socalphil/IC705BTXPA125B/UNVR67X12pt7b.h

const uint8_t UNVR67X12pt7bBitmaps[] PROGMEM = {
  0x00, 0xFF, 0xFF, 0xFF, 0xFF, 0xF0, 0x3F, 0xE0, 0xEF, 0xDF, 0xBF, 0x7E,
  0xFD, 0xC0, 0x03, 0x30, 0x77, 0x06, 0x60, 0x66, 0x0C, 0xC3, 0xFF, 0x3F,
  0xF1, 0x98, 0x19, 0x81, 0x98, 0x33, 0x0F, 0xFC, 0xFF, 0xC6, 0x60, 0x66,
  0x0E, 0xE0, 0xCC, 0x00, 0x18, 0x18, 0x18, 0x3E, 0xFF, 0xE7, 0xE7, 0xF0,
  0x7C, 0x1E, 0x0F, 0xE7, 0xE7, 0xFF, 0x7C, 0x18, 0x18, 0x18, 0x78, 0x63,
  0xF1, 0x8C, 0xC6, 0x33, 0x30, 0xCC, 0xC3, 0x36, 0x0C, 0xD8, 0x3F, 0x60,
  0x7B, 0x78, 0x0F, 0xF0, 0x6C, 0xC1, 0xB3, 0x0C, 0xCC, 0x33, 0x30, 0xCC,
  0xC6, 0x3F, 0x18, 0x78, 0xC0, 0x00, 0x1F, 0x00, 0xFE, 0x07, 0x1C, 0x1C,
  0x70, 0x71, 0xC1, 0xCE, 0x03, 0xF8, 0x07, 0x80, 0x3E, 0x19, 0xF8, 0x6E,
  0x71, 0xB8, 0xEE, 0xE1, 0xF3, 0x83, 0xCF, 0x0E, 0x1F, 0xFC, 0x1F, 0x38,
  0xFF, 0xFF, 0xC0, 0x36, 0x66, 0x4C, 0xCC, 0xCC, 0xCC, 0xCC, 0x66, 0x66,
  0x30, 0xC6, 0x66, 0x63, 0x33, 0x33, 0x33, 0x33, 0x66, 0x66, 0xC0, 0x28,
  0xD8, 0xE7, 0xFF, 0xE7, 0x1B, 0x14, 0x06, 0x00, 0x60, 0x06, 0x00, 0x60,
  0x06, 0x0F, 0xFF, 0xFF, 0xF0, 0x60, 0x06, 0x00, 0x60, 0x06, 0x00, 0x60,
  0x77, 0xEE, 0xEC, 0xFC, 0xFF, 0x80, 0x33, 0x33, 0x36, 0x66, 0x66, 0x66,
  0x66, 0xCC, 0xCC, 0xC0, 0x3E, 0x3F, 0xBF, 0xFC, 0x7E, 0x3F, 0x1F, 0x8F,
  0xC7, 0xE3, 0xF1, 0xF8, 0xFC, 0x7E, 0x3F, 0x1F, 0xFE, 0xFE, 0x3E, 0x00,
  0x3B, 0xFF, 0xFB, 0x9C, 0xE7, 0x39, 0xCE, 0x73, 0x9C, 0xE7, 0x38, 0x3E,
  0x3F, 0xBF, 0xFC, 0x7E, 0x38, 0x1C, 0x0E, 0x0E, 0x07, 0x07, 0x07, 0x07,
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
  {   609,   8,  17,  11,    2,  -16 },   // 0x46 'F'
  {   626,  10,  17,  13,    1,  -16 },   // 0x47 'G'
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

const GFXfont UNVR67X12pt7b PROGMEM = {
  (uint8_t  *)UNVR67X12pt7bBitmaps,
  (GFXglyph *)UNVR67X12pt7bGlyphs,
  0x20, 0x7E, 28 };

// Approx. 2232 bytes
