socalphil/IC705BTXPA125B/UNVR67X20pt7b.h

const uint8_t UNVR67X20pt7bBitmaps[] PROGMEM = {
  0x00, 0xFF, 0xFF, 0xFF, 0xFF, 0xFF, 0xFF, 0xFF, 0xFF, 0xFF, 0xFF, 0xFB,
  0xDC, 0x00, 0x03, 0xFF, 0xFF, 0xFE, 0xFC, 0xFF, 0xF3, 0xFF, 0xCF, 0xFF,
  0x3F, 0xFC, 0xFD, 0xF1, 0xF7, 0x87, 0x9E, 0x1E, 0x78, 0x79, 0xE1, 0xE0,
  0x00, 0x78, 0xF0, 0x07, 0x8F, 0x00, 0x70, 0xE0, 0x0F, 0x1E, 0x00, 0xE1,
  0xC0, 0x0E, 0x1C, 0x01, 0xE3, 0xC0, 0xFF, 0xFF, 0x1F, 0xFF, 0xF1, 0xFF,
  0xFE, 0x03, 0x87, 0x00, 0x38, 0x70, 0x07, 0x8F, 0x00, 0x70, 0xE0, 0x07,
  0x0E, 0x00, 0xF1, 0xE0, 0x0E, 0x1C, 0x07, 0xFF, 0xF8, 0xFF, 0xFF, 0x8F,
  0xFF, 0xF0, 0x1C, 0x38, 0x03, 0xC7, 0x80, 0x38, 0x70, 0x03, 0x87, 0x00,
  0x78, 0xF0, 0x07, 0x0E, 0x00, 0xF1, 0xE0, 0x0F, 0x1E, 0x00, 0x0F, 0x00,
  0x78, 0x03, 0xC0, 0x1E, 0x01, 0xFC, 0x1F, 0xF9, 0xFF, 0xFF, 0x1F, 0xF8,
  0xFF, 0xC7, 0xFF, 0x00, 0xFE, 0x07, 0xFC, 0x0F, 0xF0, 0x3F, 0xC0, 0x7F,
  0x00, 0xFF, 0xC7, 0xFE, 0x3F, 0xF1, 0xFF, 0xFF, 0x3F, 0xF0, 0x7F, 0x01,
  0xE0, 0x0F, 0x00, 0x78, 0x03, 0xC0, 0x1E, 0x00, 0x3E, 0x00, 0xE0, 0xFE,
  0x01, 0x83, 0xFE, 0x07, 0x07, 0xBC, 0x0C, 0x0F, 0x78, 0x38, 0x1E, 0xF0,
  0x70, 0x3D, 0xE0, 0xC0, 0x7B, 0xC3, 0x80, 0xF3, 0x86, 0x01, 0xE7, 0x1C,
  0x03, 0xCE, 0x30, 0x07, 0x9C, 0xE0, 0x0F, 0xF9, 0x8F, 0x8F, 0xE7, 0x3F,
  0x8F, 0x8C, 0xFF, 0x80, 0x39, 0xEF, 0x00, 0x73, 0xDE, 0x00, 0xC7, 0xBC,
  0x03, 0x8F, 0x78, 0x06, 0x1E, 0xF0, 0x1C, 0x3D, 0xE0, 0x30, 0x7B, 0xC0,
  0xE0, 0xF7, 0x81, 0x81, 0xEF, 0x07, 0x03, 0xFE, 0x0E, 0x03, 0xF8, 0x18,
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
  {  1546,  13,  27,  17,    3,  -26 },   // 0x46 'F'
  {  1590,  17,  27,  22,    2,  -26 },   // 0x47 'G'
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

const GFXfont UNVR67X20pt7b PROGMEM = {
  (uint8_t  *)UNVR67X20pt7bBitmaps,
  (GFXglyph *)UNVR67X20pt7bGlyphs,
  0x20, 0x7E, 47 };

// Approx. 4672 bytes
