socalphil/IC705BTXPA125B/UNVR67X7pt7b.h

const uint8_t UNVR67X7pt7bBitmaps[] PROGMEM = {
  0x00, 0xFF, 0xFC, 0xF0, 0xB6, 0xD0, 0x12, 0x6C, 0x93, 0xF6, 0xCD, 0xBF,
  0x24, 0xD9, 0x20, 0x21, 0x1F, 0xBE, 0x38, 0x7B, 0xF1, 0x08, 0xE4, 0xA4,
  0xA4, 0xA8, 0xE8, 0x17, 0x15, 0x15, 0x25, 0x27, 0x30, 0xF1, 0xE3, 0xC3,
  0x5E, 0xB7, 0x6E, 0xCC, 0xEC, 0xFF, 0x7F, 0xFF, 0xF4, 0xBF, 0xFF, 0xF8,
  0x26, 0xF6, 0x60, 0x10, 0x20, 0x47, 0xF1, 0x02, 0x04, 0x00, 0xFA, 0xF0,
  0xF0, 0x24, 0xA4, 0x92, 0x92, 0x00, 0x77, 0xF7, 0xBD, 0xEF, 0x7B, 0xFB,
  0x80, 0x7F, 0xB6, 0xDB, 0x6C, 0x77, 0xF6, 0x31, 0x19, 0x88, 0xFF, 0xC0,
  0xF7, 0xC6, 0x33, 0x9C, 0x7B, 0xFB, 0x80, 0x38, 0xE7, 0x9E, 0x7B, 0x6F,
  0xFF, 0x18, 0x60, 0xFF, 0xF1, 0xFF, 0xEC, 0x7B, 0xFB, 0x80, 0x7F, 0xF1,
  0xFF, 0xEF, 0x7B, 0xFB, 0x80, 0xFF, 0xC6, 0x33, 0x18, 0xC6, 0x63, 0x00,
  0x77, 0xF7, 0xF7, 0x6F, 0x7B, 0xFB, 0x80, 0x77, 0xF7, 0xBF, 0xFC, 0x7B,
  0xFB, 0x80, 0xF0, 0x3C, 0xF0, 0xFA, 0x01, 0x06, 0x18, 0x70, 0xC0, 0x70,
  0x18, 0x06, 0x01, 0xFC, 0x0F, 0xC0, 0x80, 0x60, 0x18, 0x0E, 0x03, 0x0E,
  0x18, 0x60, 0x80, 0x76, 0xC6, 0x33, 0x10, 0x80, 0x63, 0x00, 0x3E, 0x43,
  0x81, 0xBD, 0xAD, 0xAD, 0xAD, 0xAD, 0xBF, 0x80, 0xC0, 0x7C, 0x30, 0xE3,
  0x9E, 0x79, 0xE7, 0xDF, 0xCF, 0x30, 0xFB, 0xFC, 0xF3, 0xFB, 0xFC, 0xF3,
  0xFF, 0xE0, 0x7B, 0xFC, 0xF0, 0xC3, 0x0C, 0x33, 0xFD, 0xE0, 0xFD, 0xFF,
  0x1E, 0x3C, 0x78, 0xF1, 0xE3, 0xFF, 0xF8, 0xFF, 0xF1, 0x8F, 0xFF, 0x18,
  0xFF, 0xC0, 0xFF, 0xF1, 0x8F, 0xFF, 0x18, 0xC6, 0x00, 0x7D, 0xFF, 0x1E,
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
  {   218,   5,  10,   6,    0,   -9 },   // 0x46 'F'
  {   225,   7,  10,   8,    0,   -9 },   // 0x47 'G'
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

const GFXfont UNVR67X7pt7b PROGMEM = {
  (uint8_t  *)UNVR67X7pt7bBitmaps,
  (GFXglyph *)UNVR67X7pt7bGlyphs,
  0x20, 0x7E, 16 };

// Approx. 1269 bytes
