socalphil/IC705BTXPA125B/jpeg1.h

// We need this header file to use FLASH as storage with PROGMEM directive on the Mega


// Here is the 320 x 480 jpeg image data
const uint8_t Baboon40[] PROGMEM = {
0xFF,0xD8,0xFF,0xE0,0x00,0x10,0x4A,0x46,0x49,0x46,0x00,0x01,0x01,0x00,0x00,0x01,0x00,0x01,0x00,0x00,0xFF,0xDB,0x00,0x43,0x00,0x14,0x0E,0x0F,0x12,0x0F,0x0D,0x14,
0x12,0x10,0x12,0x17,0x15,0x14,0x18,0x1E,0x32,0x21,0x1E,0x1C,0x1C,0x1E,0x3D,0x2C,0x2E,0x24,0x32,0x49,0x40,0x4C,0x4B,0x47,0x40,0x46,0x45,0x50,0x5A,0x73,0x62,0x50,
0x55,0x6D,0x56,0x45,0x46,0x64,0x88,0x65,0x6D,0x77,0x7B,0x81,0x82,0x81,0x4E,0x60,0x8D,0x97,0x8C,0x7D,0x96,0x73,0x7E,0x81,0x7C,0xFF,0xDB,0x00,0x43,0x01,0x15,0x17,
0x17,0x1E,0x1A,0x1E,0x3B,0x21,0x21,0x3B,0x7C,0x53,0x46,0x53,0x7C,0x7C,0x7C,0x7C,0x7C,0x7C,0x7C,0x7C,0x7C,0x7C,0x7C,0x7C,0x7C,0x7C,0x7C,0x7C,0x7C,0x7C,0x7C,0x7C,
0x7C,0x7C,0x7C,0x7C,0x7C,0x7C,0x7C,0x7C,0x7C,0x7C,0x7C,0x7C,0x7C,0x7C,0x7C,0x7C,0x7C,0x7C,0x7C,0x7C,0x7C,0x7C,0x7C,0x7C,0x7C,0x7C,0x7C,0x7C,0x7C,0x7C,0xFF,0xC0,
0x00,0x11,0x08,0x01,0xE0,0x01,0x40,0x03,0x01,0x22,0x00,0x02,0x11,0x01,0x03,0x11,0x01,0xFF,0xC4,0x00,0x1A,0x00,0x00,0x03,0x01,0x01,0x01,0x01,0x00,0x00,0x00,0x00,
0x00,0x00,0x00,0x00,0x00,0x00,0x02,0x03,0x04,0x01,0x05,0x00,0x06,0xFF,0xC4,0x00,0x3E,0x10,0x00,0x02,0x02,0x01,0x03,0x02,0x04,0x03,0x06,0x06,0x01,0x03,0x04,0x01,
0x05,0x00,0x01,0x02,0x03,0x11,0x00,0x12,0x21,0x31,0x04,0x41,0x13,0x22,0x51,0x61,0x71,0x81,0x91,0x05,0x32,0x42,0xA1,0xB1,0xC1,0x14,0x23,0x52,0xD1,0xE1,0xF0,0x62,
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
0x34,0x00,0xB9,0x7F,0x0F,0x83,0xBF,0x6F,0x6F,0x5C,0x6C,0x53,0x29,0x85,0xA3,0x11,0xC4,0xAA,0x87,0x6D,0x64,0xEE,0x72,0xB6,0x68,0xFA,0x78,0xBC,0x36,0xD0,0xED,0xDD,
0x7B,0x0F,0x97,0x6C,0x91,0xD2,0x31,0x37,0x89,0x23,0xC4,0xCB,0xA7,0x86,0x3C,0x1F,0x4D,0xB0,0x50,0xD7,0x62,0x14,0x3B,0x33,0x13,0x2C,0x51,0xA8,0xE3,0x4E,0xDF,0x20,
0x33,0x60,0x3E,0x1C,0xA1,0x84,0x7F,0xCD,0xEF,0xA8,0xF3,0x77,0xBF,0xE9,0x8D,0x85,0xE3,0x94,0x96,0x0A,0xBA,0xF4,0x81,0xA0,0x02,0x58,0x7C,0x31,0x88,0x92,0xC8,0x2D,
0x3A,0x70,0xE4,0x7E,0x27,0x7B,0x35,0xF0,0xCD,0x41,0xB2,0x47,0x46,0xD4,0xA1,0x23,0x20,0x6A,0x1E,0x5B,0xFB,0xDF,0xED,0x63,0x57,0xA7,0x11,0xC5,0x1B,0xA4,0xC5,0x5E,
0xC8,0x65,0x63,0xC1,0xCB,0x4F,0x4D,0x34,0xD2,0x23,0x89,0x82,0xBA,0x9D,0xD5,0x8F,0xEF,0x9E,0x6E,0x95,0x14,0xAB,0x32,0x30,0xD3,0xBD,0x06,0xD8,0x9F,0x8F,0x6C,0xD4,
0x0B,0x22,0xD0,0xD2,0xA9,0x37,0x6B,0x7B,0xA9,0x5A,0xA3,0x5B,0x92,0x32,0x8F,0xE1,0xA1,0x94,0xAA,0xAC,0xBA,0xD5,0x29,0x6B,0xB7,0xC8,0xE5,0x12,0xC6,0x91,0x96,0x2F,
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
};
