socalphil/IC705BTXPA125B/FreeSerif6pt7b.h

const uint8_t FreeSerif6pt7bBitmaps[] PROGMEM = {
  0x00, 0xF1, 0xB6, 0x80, 0x28, 0xA0, 0x82, 0x41, 0x05, 0x14, 0x06, 0x88,
  0xC3, 0x11, 0x90, 0x64, 0x94, 0x80, 0x88, 0x54, 0x08, 0x29, 0x02, 0x10,
  0x12, 0x0C, 0x02, 0x65, 0xA2, 0x41, 0x10, 0xFE, 0x80, 0x02, 0x49, 0x24,
  0x00, 0x00, 0x92, 0x49, 0x00, 0x09, 0x09, 0x00, 0x10, 0x41, 0x04, 0x10,
  0x40, 0x80, 0xE0, 0x80, 0x24, 0xA4, 0xA4, 0x11, 0x2C, 0xA3, 0x8E, 0x24,
  0x92, 0x26, 0x66, 0x66, 0x66, 0x70, 0x20, 0x82, 0x10, 0x00, 0x5E, 0x70,
  0x40, 0x20, 0x84, 0x3A, 0x00, 0x43, 0x14, 0x13, 0xF1, 0x04, 0x3A, 0x18,
  0x20, 0x84, 0x3A, 0x10, 0x84, 0x1E, 0xCB, 0x24, 0x92, 0x7C, 0x42, 0x01,
  0x08, 0x04, 0xA9, 0x96, 0x29, 0x99, 0x52, 0x63, 0x94, 0x84, 0x44, 0x88,
  0x80, 0xC8, 0x04, 0x66, 0x10, 0x18, 0x10, 0xFC, 0x00, 0x3F, 0xC0, 0xC0,
  0xC3, 0x33, 0x00, 0xA9, 0x12, 0x00, 0x04, 0x16, 0x20, 0x93, 0x92, 0x59,
  0x42, 0xA9, 0x00, 0x64, 0x00, 0x18, 0x18, 0x04, 0x24, 0x06, 0x42, 0x43,
  0x78, 0xC9, 0x9B, 0x26, 0x4C, 0x58, 0xB6, 0x3E, 0x85, 0x06, 0x0C, 0x08,
  0x10, 0x19, 0x78, 0x42, 0x43, 0x41, 0x41, 0x41, 0x42, 0x6C, 0x7C, 0x81,
  0x02, 0x24, 0x48, 0x10, 0xB3, 0x7D, 0x04, 0x11, 0x45, 0x04, 0x18, 0x3E,
  0x40, 0x40, 0xC0, 0xC3, 0x43, 0x43, 0x32, 0x67, 0x42, 0x42, 0x42, 0x42,
  0x42, 0x42, 0x62, 0x66, 0x66, 0x66, 0x66, 0x72, 0x22, 0x22, 0x2A, 0x66,
  0x32, 0x1A, 0x0E, 0x07, 0x83, 0x61, 0x98, 0xC6, 0x60, 0x81, 0x02, 0x04,
  0x08, 0x10, 0xB3, 0x60, 0xD8, 0x67, 0x09, 0x4A, 0x50, 0x93, 0x24, 0xC9,
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
  {   173,   6,   8,   7,    0,   -7 },   // 0x46 'F'
  {   179,   8,   8,   8,    0,   -7 },   // 0x47 'G'
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

const GFXfont FreeSerif6pt7b PROGMEM = {
  (uint8_t  *)FreeSerif6pt7bBitmaps,
  (GFXglyph *)FreeSerif6pt7bGlyphs,
  0x20, 0x7E, 20 };

// Approx. 1150 bytes
