socalphil/IC705BTXPA125B/BT.h

// array size is 957
static const uint8_t BT[] PROGMEM  = {
  0xff, 0xd8, 0xff, 0xe0, 0x00, 0x10, 0x4a, 0x46, 0x49, 0x46, 0x00, 0x01, 0x01, 0x01, 0x00, 0x60, 
  0x00, 0x60, 0x00, 0x00, 0xff, 0xdb, 0x00, 0x43, 0x00, 0x03, 0x02, 0x02, 0x03, 0x02, 0x02, 0x03, 
  0x03, 0x03, 0x03, 0x04, 0x03, 0x03, 0x04, 0x05, 0x08, 0x05, 0x05, 0x04, 0x04, 0x05, 0x0a, 0x07, 
  0x07, 0x06, 0x08, 0x0c, 0x0a, 0x0c, 0x0c, 0x0b, 0x0a, 0x0b, 0x0b, 0x0d, 0x0e, 0x12, 0x10, 0x0d, 
  0x0e, 0x11, 0x0e, 0x0b, 0x0b, 0x10, 0x16, 0x10, 0x11, 0x13, 0x14, 0x15, 0x15, 0x15, 0x0c, 0x0f, 
  0x17, 0x18, 0x16, 0x14, 0x18, 0x12, 0x14, 0x15, 0x14, 0xff, 0xdb, 0x00, 0x43, 0x01, 0x03, 0x04, 
  0x04, 0x05, 0x04, 0x05, 0x09, 0x05, 0x05, 0x09, 0x14, 0x0d, 0x0b, 0x0d, 0x14, 0x14, 0x14, 0x14, 
  0x14, 0x14, 0x14, 0x14, 0x14, 0x14, 0x14, 0x14, 0x14, 0x14, 0x14, 0x14, 0x14, 0x14, 0x14, 0x14, 
  0x14, 0x14, 0x14, 0x14, 0x14, 0x14, 0x14, 0x14, 0x14, 0x14, 0x14, 0x14, 0x14, 0x14, 0x14, 0x14, 
  0x14, 0x14, 0x14, 0x14, 0x14, 0x14, 0x14, 0x14, 0x14, 0x14, 0x14, 0x14, 0x14, 0x14, 0xff, 0xc0, 
  0x00, 0x11, 0x08, 0x00, 0x18, 0x00, 0x14, 0x03, 0x01, 0x22, 0x00, 0x02, 0x11, 0x01, 0x03, 0x11, 
  0x01, 0xff, 0xc4, 0x00, 0x1f, 0x00, 0x00, 0x01, 0x05, 0x01, 0x01, 0x01, 0x01, 0x01, 0x01, 0x00, 
  0x00, 0x00, 0x00, 0x00, 0x00, 0x00, 0x00, 0x01, 0x02, 0x03, 0x04, 0x05, 0x06, 0x07, 0x08, 0x09, 
  0x0a, 0x0b, 0xff, 0xc4, 0x00, 0xb5, 0x10, 0x00, 0x02, 0x01, 0x03, 0x03, 0x02, 0x04, 0x03, 0x05, 
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
  0xfa, 0xff, 0xda, 0x00, 0x0c, 0x03, 0x01, 0x00, 0x02, 0x11, 0x03, 0x11, 0x00, 0x3f, 0x00, 0x74, 
  0x5a, 0x5e, 0xa3, 0x71, 0xa3, 0xcf, 0xab, 0x47, 0x65, 0x3c, 0x9a, 0x65, 0xbc, 0xab, 0x0c, 0xb7, 
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
};
